elfchief/powerfreq-hardware/LTspice/60_Hz_zero_cross_detector_simple_120v.asc

C1: cap; 100n
C2: cap; 10n
C5: cap; 10n
D1: diode; 1N4148
D2: diode; 1N4148
D3: diode; 1N4148
D4: diode; 1N4148
D5: diode; 1N4148
Q1: npn; 2N3904
Q2: npn; 2N3904
R1: res; 2k
R10: res; 1k
R11: res; 2.2k
R13: res; 20k
R16: res; 1k
R17: res; 250
V1: voltage; SINE(0 170 60); AC 1
V4: voltage; 5
Named nets: 0, IN, +5, CLAMP, 60pps, TRIG
V1 = isolated 120 Vrms transformer winding (second 
primary of a small 120/240v dual-primary transformer)
.tran 0 70m 0 100n
Slew rate 
@ zero cross 
~0.013v/uS
With C1 = 100n, C5 = 10n:
~115uS 5v pulse at every pos zero cross
Tr  ~350nS    Td ~233uS
 
With C1 = C5 = 0:
~100 uS pulse    Tr ~350nS     Td ~19.3uS
;ac dec 100 10 10k
1 watt
2 watt
Filter Fc ~475Hz
12dB/8ve
60 Hz
120Vrms
170Vpk
For Fc ~ 475Hz:
C1=100n, C5=10n
 
For Fc ~ 95Hz:
C1=500n, C5=50n
